glydeck/Analog-ESR-Meter/images/IMG_0498.jpg

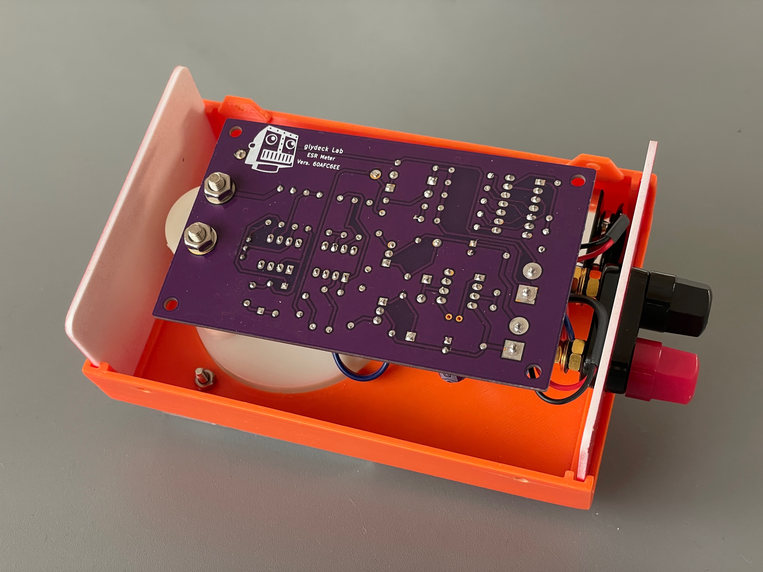
images/IMG_0498.jpg
